ieiao/JAC/fw/components/jac/drivers/resources.h

#ifndef __RESOURCES_H__
#define __RESOURCES_H__

int resources_init(void);
void resources_deinit(void);

extern const uint8_t *u8g2_font_logisoso62_tn;
extern const uint8_t *u8g2_font_logisoso28_tn;
extern const uint8_t *u8g2_font_wqy16_t_gb2312a;
extern const uint8_t *u8g2_font_siji_t_6x10;
extern const uint8_t *u8g2_font_luIS12;
extern const uint8_t *u8g2_font_luIS24;
extern const uint8_t *u8g2_font_luRS10;
extern const uint8_t *u8g2_font_courR10;
extern const uint8_t *u8g2_font_helvR10;
extern const uint8_t *xbm_tree;
extern const uint8_t *xbm_batt_dead;
extern const uint8_t *xbm_jac_p1;
extern const uint8_t *xbm_jac_p2;
extern const uint8_t *xbm_jac_p3;

#endif
